Triggertrap/triggertrap-ada/Ada Graphics/Ada Sensor Icons/PDF/fb_890_ada_icon- sound.pdf

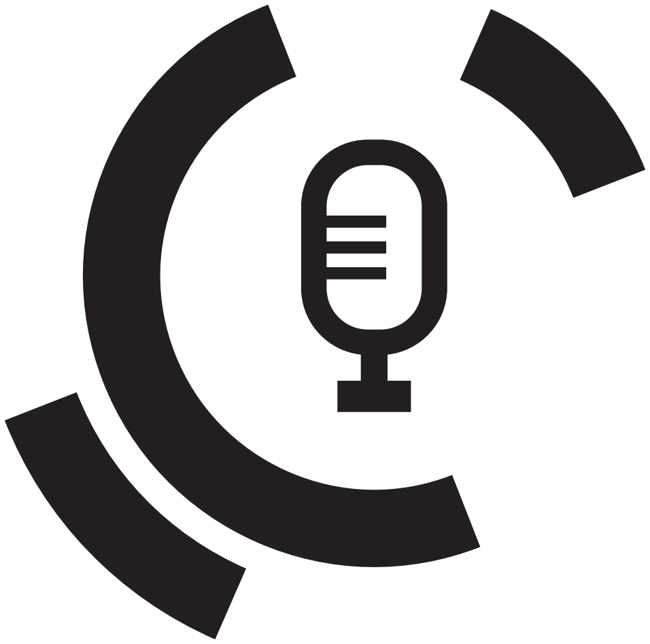
[picture p1: figure]
