Triggertrap/triggertrap-ada/Ada Graphics/Ada Sensor Icons/PDF/fb_890_ada_icon-ambient.pdf

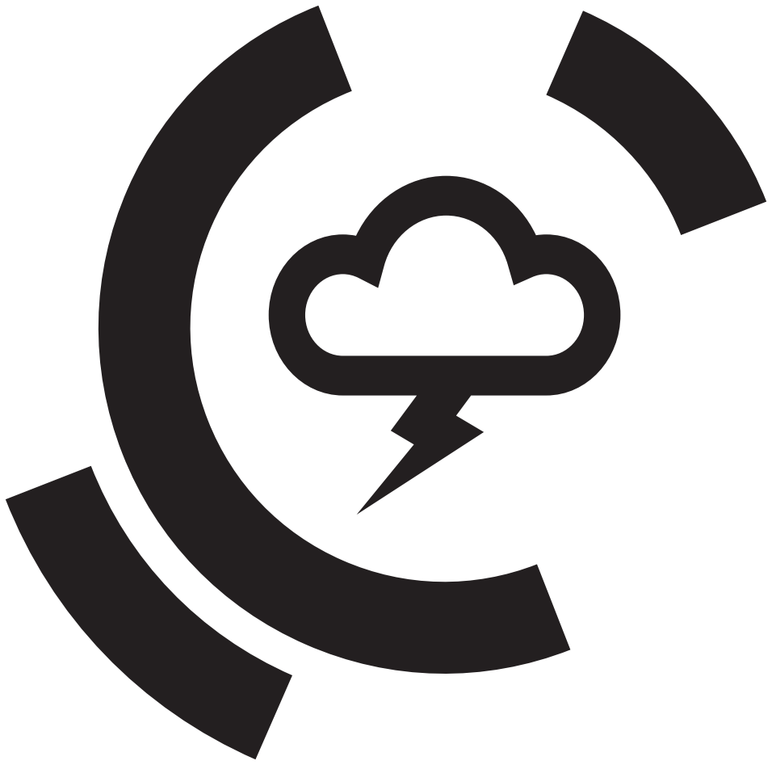
[picture p2: figure]
