Triggertrap/triggertrap-ada/Ada Graphics/Ada Sensor Icons/PDF/fb_890_ada_icon-laser.pdf

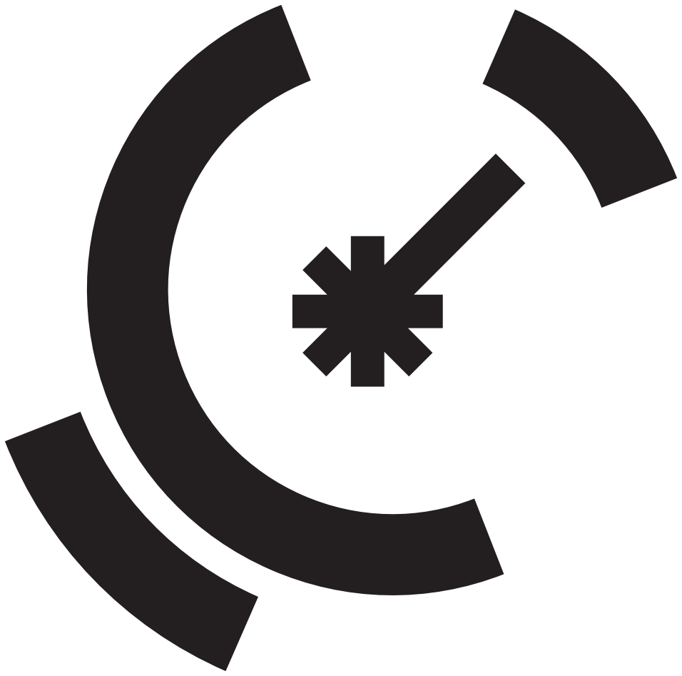
[picture p3: figure]
