Triggertrap/triggertrap-ada/Ada Graphics/Ada Sensor Icons/PDF/fb_890_ada_icon-pir.pdf

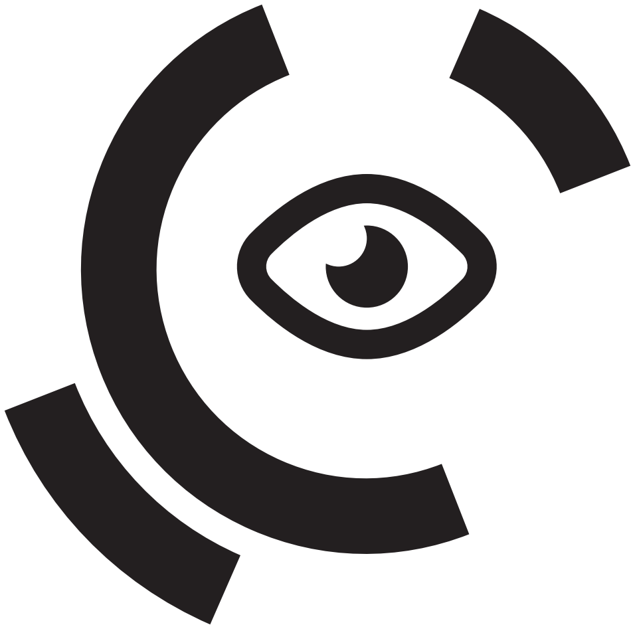
[picture p4: figure]
