Triggertrap/triggertrap-ada/Ada Casing/TT-Issue-A_PDF_mfg_notes/TT-100-A_ADA_BASE_FULL_ASSEMBLY DRG.PDF

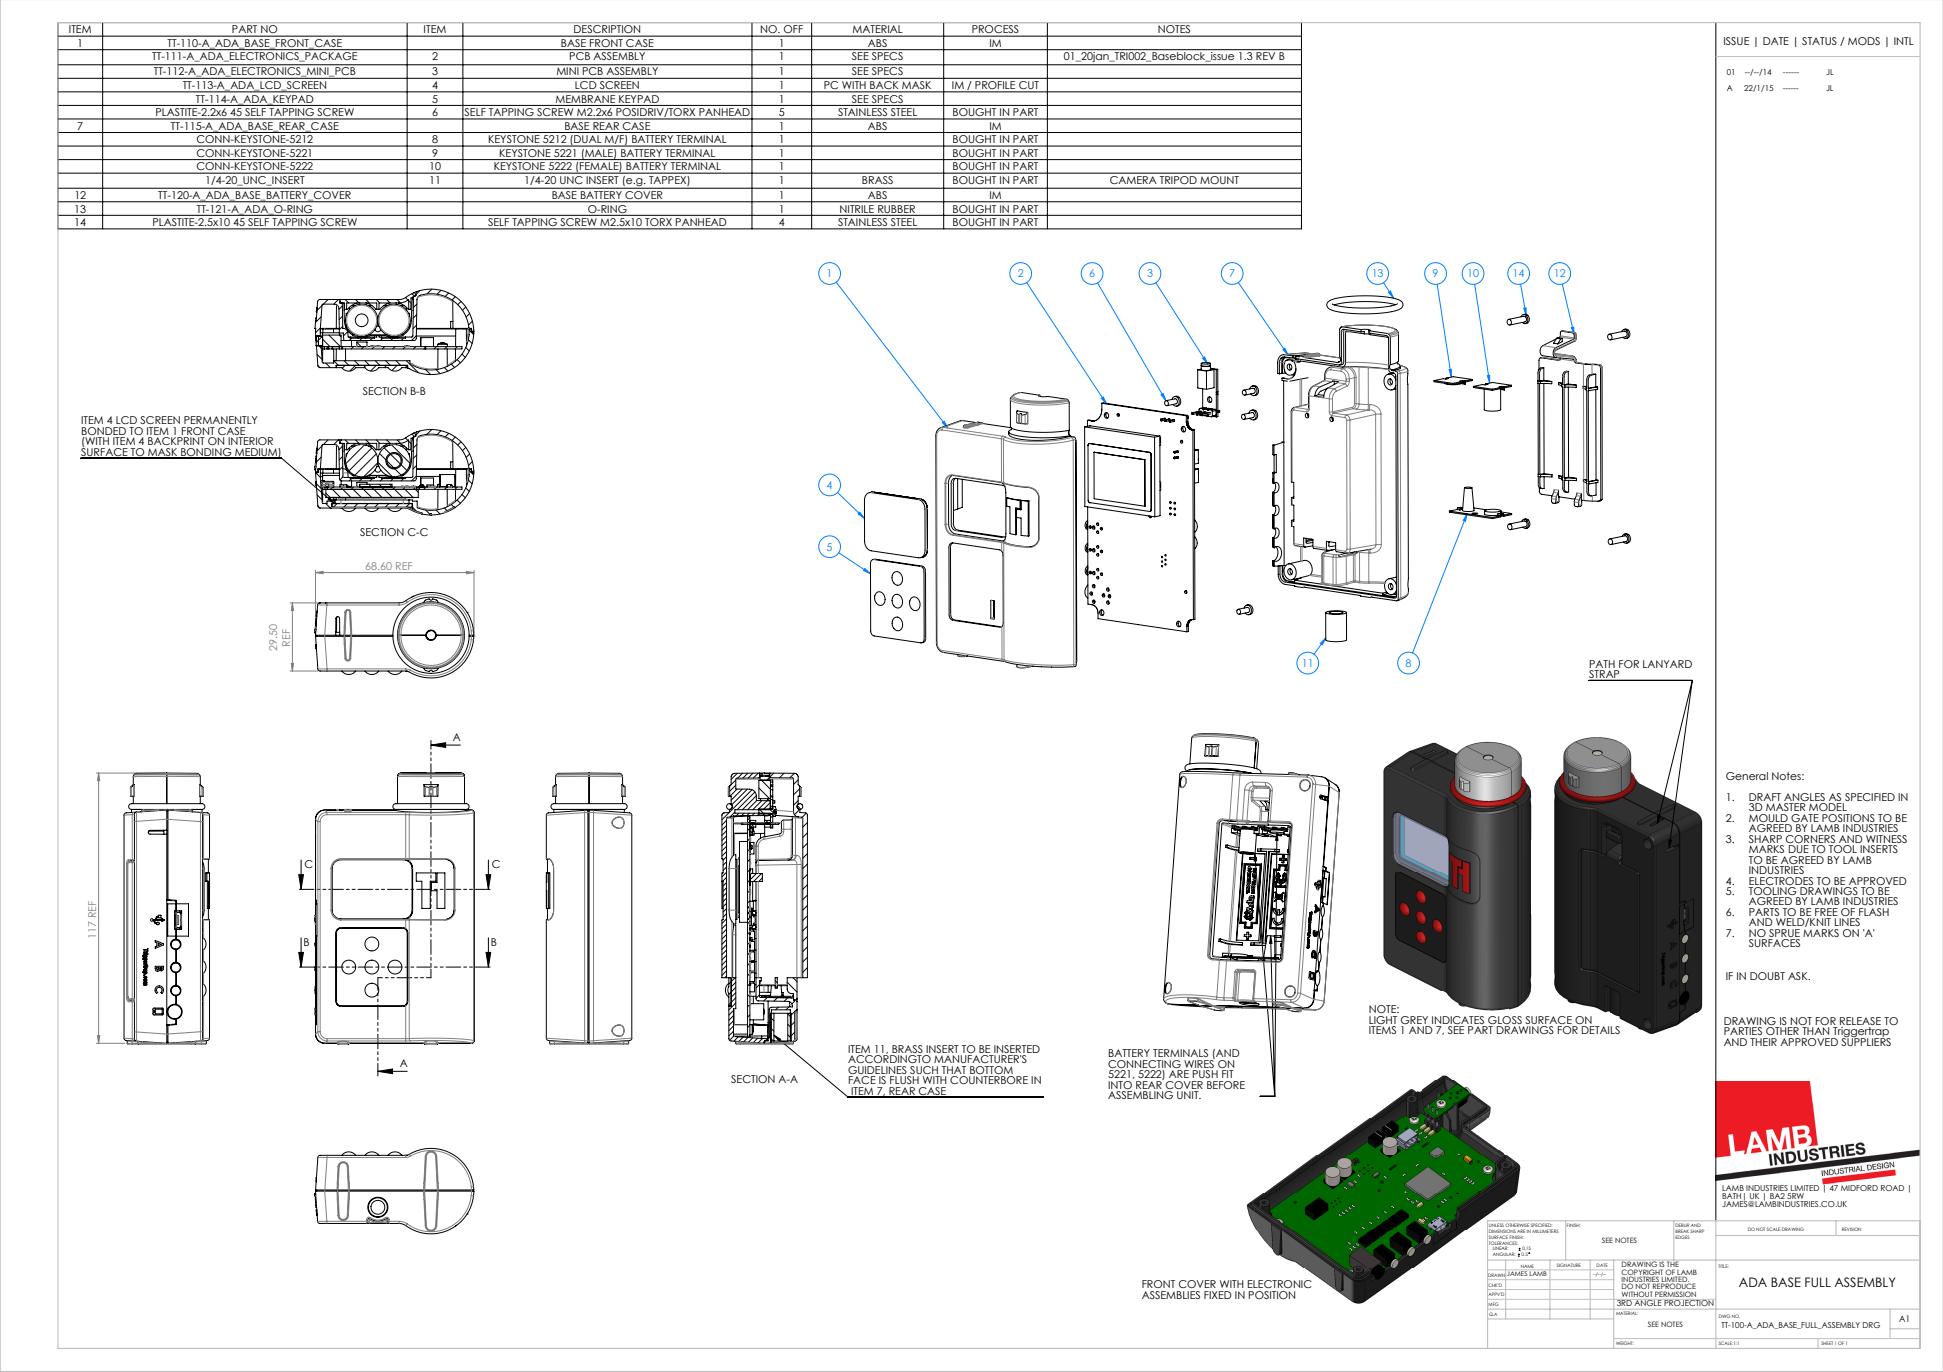
[picture p16: page 1]
117 REF; 68.60 REF; SECTION B-B; SECTION A-A; SECTION C-C; SEE NOTES; SCALE:1:1; SHEET 1 OF 1; DO NOT SCALE DRAWING; REVISION; DEBUR AND BREAK SHARP; UNLESS OTHERWISE SPECIFIED:; FINISH:

ITEM | PART NO | ITEM | DESCRIPTION | NO. OFF | MATERIAL | PROCESS | NOTES | ISSUE | DATE | STATUS / MODS | INTL
1 | TT-110-A_ADA_BASE_FRONT_CASE | | BASE FRONT CASE | 1 | ABS | IM

TT-111-A_ADA_ELECTRONICS_PACKAGE | 2 | PCB ASSEMBLY | 1 | SEE SPECS | | 01_20jan_TRI002_Baseblock_issue 1.3 REV B
TT-112-A_ADA_ELECTRONICS_MINI_PCB | 3 | MINI PCB ASSEMBLY | 1 | SEE SPECS
TT-113-A_ADA_LCD_SCREEN | 4 | LCD SCREEN | 1 | PC WITH BACK MASK | IM / PROFILE CUT
TT-114-A_ADA_KEYPAD | 5 | MEMBRANE KEYPAD | 1 | SEE SPECS
PLASTITE-2.2x6 45 SELF TAPPING SCREW | 6 | SELF TAPPING SCREW M2.2x6 POSIDRIV/TORX PANHEAD | 5 | STAINLESS STEEL | BOUGHT IN PART
CONN-KEYSTONE-5212 | 8 | KEYSTONE 5212 (DUAL M/F) BATTERY TERMINAL | 1 | | BOUGHT IN PART
CONN-KEYSTONE-5221 | 9 | KEYSTONE 5221 (MALE) BATTERY TERMINAL | 1 | | BOUGHT IN PART
CONN-KEYSTONE-5222 | 10 | KEYSTONE 5222 (FEMALE) BATTERY TERMINAL | 1 | | BOUGHT IN PART
1/4-20_UNC_INSERT | 11 | 1/4-20 UNC INSERT (e.g. TAPPEX) | 1 | BRASS | BOUGHT IN PART | CAMERA TRIPOD MOUNT

7 | TT-115-A_ADA_BASE_REAR_CASE | | BASE REAR CASE | 1 | ABS | IM

12 | TT-120-A_ADA_BASE_BATTERY_COVER | | BASE BATTERY COVER | 1 | ABS | IM
13 | TT-121-A_ADA_O-RING | | O-RING | 1 | NITRILE RUBBER | BOUGHT IN PART
14 | PLASTITE-2.5x10 45 SELF TAPPING SCREW | | SELF TAPPING SCREW M2.5x10 TORX PANHEAD | 4 | STAINLESS STEEL | BOUGHT IN PART

ITEM 4 LCD SCREEN PERMANENTLY
BONDED TO ITEM 1 FRONT CASE
(WITH ITEM 4 BACKPRINT ON INTERIOR
SURFACE TO MASK BONDING MEDIUM)

PATH FOR LANYARD
STRAP

General Notes:
1. DRAFT ANGLES AS SPECIFIED IN
3D MASTER MODEL
2. MOULD GATE POSITIONS TO BE
AGREED BY LAMB INDUSTRIES
3. SHARP CORNERS AND WITNESS
MARKS DUE TO TOOL INSERTS
TO BE AGREED BY LAMB
INDUSTRIES
4. ELECTRODES TO BE APPROVED
5. TOOLING DRAWINGS TO BE
6. PARTS TO BE FREE OF FLASH
AND WELD/KNIT LINES
7. NO SPRUE MARKS ON 'A'
SURFACES

IF IN DOUBT ASK.

NOTE:
LIGHT GREY INDICATES GLOSS SURFACE ON
ITEMS 1 AND 7, SEE PART DRAWINGS FOR DETAILS

DRAWING IS NOT FOR RELEASE TO
PARTIES OTHER THAN Triggertrap
AND THEIR APPROVED SUPPLIERS

ITEM 11, BRASS INSERT TO BE INSERTED
ACCORDINGTO MANUFACTURER'S
GUIDELINES SUCH THAT BOTTOM
FACE IS FLUSH WITH COUNTERBORE IN
ITEM 7, REAR CASE

BATTERY TERMINALS (AND
CONNECTING WIRES ON
5221, 5222) ARE PUSH FIT
INTO REAR COVER BEFORE
ASSEMBLING UNIT.

LAMB INDUSTRIES LIMITED | 47 MIDFORD ROAD
BATH| UK | BA2 5RW
JAMES@LAMBINDUSTRIES.CO.UK

DIMENSIONS ARE IN MILLIMETERS
SURFACE FINISH:
TOLERANCES:
ANGULAR: 0.5

NAME | SIGNATURE | DATE | DRAWING IS THE COPYRIGHT OF LAMB INDUSTRIES LIMITED. DO NOT REPRODUCE WITHOUT PERMISSION | TITLE: ADA BASE FULL ASSEMBLY

DRAWN | JAMES LAMB | | --/--/--

FRONT COVER WITH ELECTRONIC
ASSEMBLIES FIXED IN POSITION

CHK'D
APPV'D
MFG | | | | 3RD ANGLE PROJECTION
Q.A | | | | MATERIAL: SEE NOTES | DWG NO. TT-100-A_ADA_BASE_FULL_ASSEMBLY DRG | A1
