Triggertrap/triggertrap-ada/Ada Casing/TT-Issue-A_PDF_mfg_notes/TT-250-A_SENSOR_pot_knob_DRG.PDF

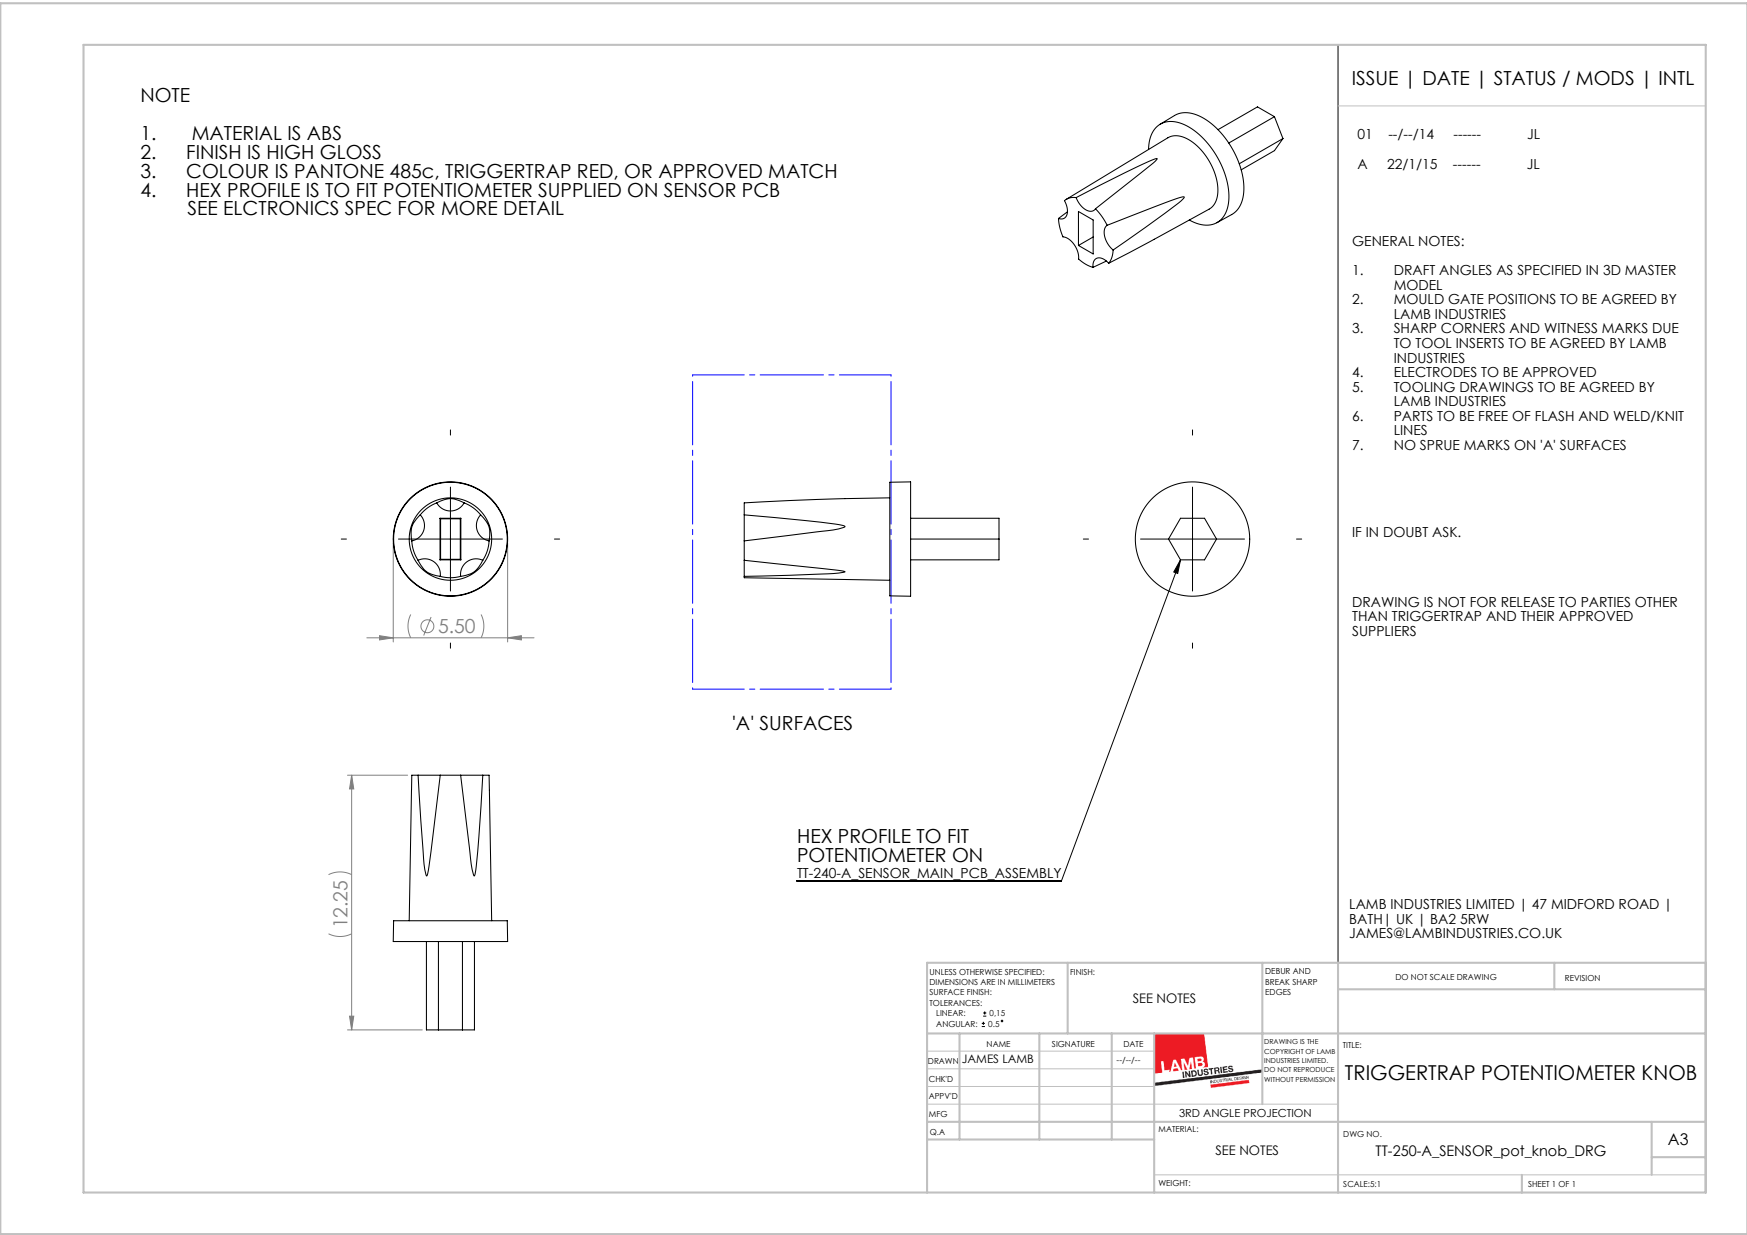
[picture p48: page 1]
'A' SURFACES; SEE NOTES; SCALE:5:1; SHEET 1 OF 1; DO NOT SCALE DRAWING; REVISION; DEBUR AND BREAK SHARP; UNLESS OTHERWISE SPECIFIED:; FINISH:

ISSUE | DATE | STATUS / MODS | INTL

NOTE
1. MATERIAL IS ABS
2. FINISH IS HIGH GLOSS
3. COLOUR IS PANTONE 485c, TRIGGERTRAP RED, OR APPROVED MATCH
4. HEX PROFILE IS TO FIT POTENTIOMETER SUPPLIED ON SENSOR PCB
SEE ELCTRONICS SPEC FOR MORE DETAIL

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

IF IN DOUBT ASK.

DRAWING IS NOT FOR RELEASE TO PARTIES OTHER
THAN TRIGGERTRAP AND THEIR APPROVED
SUPPLIERS

HEX PROFILE TO FIT
POTENTIOMETER ON
TT-240-A_SENSOR_MAIN_PCB_ASSEMBLY

LAMB INDUSTRIES LIMITED | 47 MIDFORD ROAD
BATH| UK | BA2 5RW
JAMES@LAMBINDUSTRIES.CO.UK

DIMENSIONS ARE IN MILLIMETERS
SURFACE FINISH:
TOLERANCES:
ANGULAR: 0.5

NAME | SIGNATURE | DATE | | DRAWING IS THE COPYRIGHT OF LAMB INDUSTRIES LIMITED. DO NOT REPRODUCE WITHOUT PERMISSION | TITLE: TRIGGERTRAP POTENTIOMETER KNOB

DRAWN | JAMES LAMB | | --/--/--

CHK'D
APPV'D
MFG | | | | 3RD ANGLE PROJECTION
Q.A | | | | MATERIAL: SEE NOTES | DWG NO. TT-250-A_SENSOR_pot_knob_DRG | A3
