Triggertrap/triggertrap-ada/Ada Casing/TT-Issue-A_PDF_mfg_notes/TT-260-A-ADA_MIRROR_ASSY_DRG.PDF

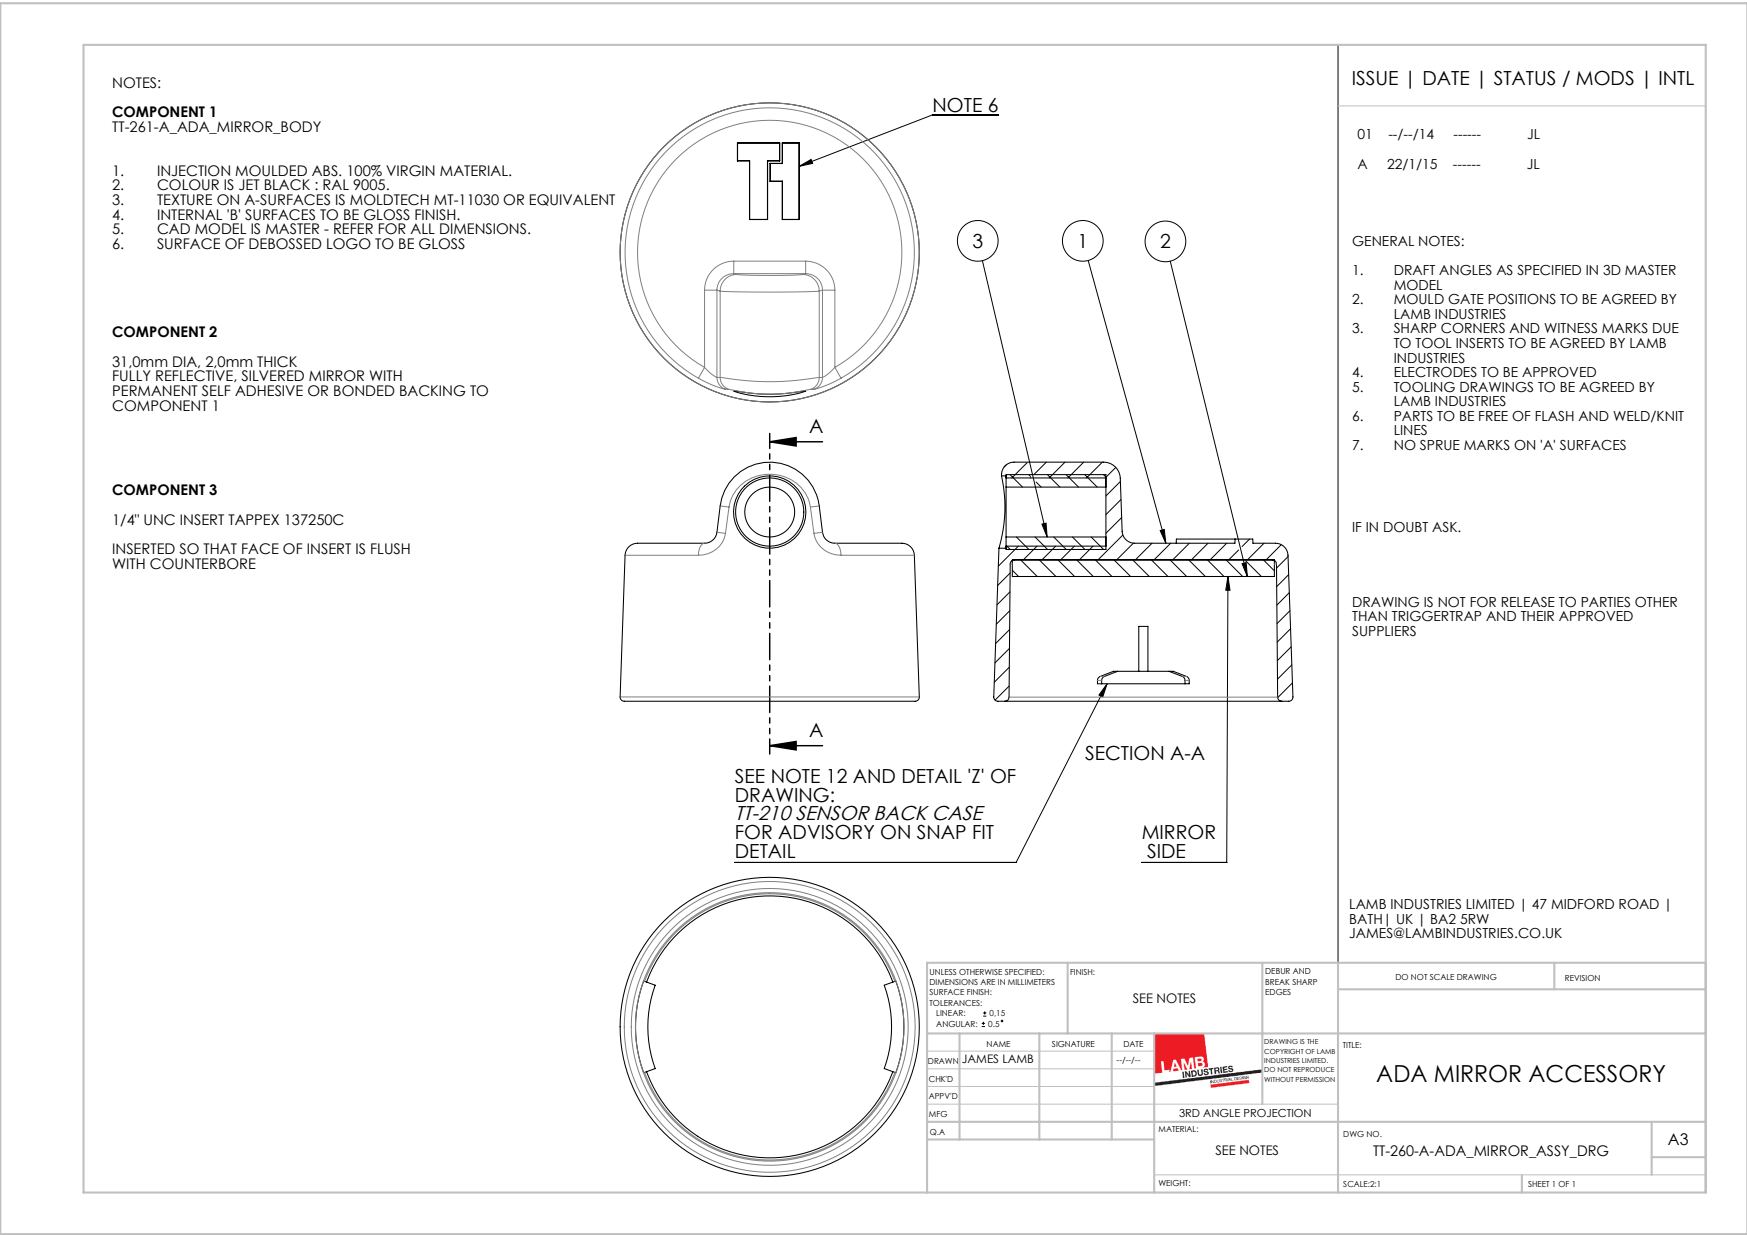
[picture p49: page 1]
NOTE 6; SECTION A-A; COMPONENT 1; SEE NOTES; SCALE:2:1; SHEET 1 OF 1; DO NOT SCALE DRAWING; REVISION; DEBUR AND BREAK SHARP; UNLESS OTHERWISE SPECIFIED:; FINISH:

ISSUE | DATE | STATUS / MODS | INTL

1. INJECTION MOULDED ABS. 100% VIRGIN MATERIAL.
2. COLOUR IS JET BLACK : RAL 9005.
3. TEXTURE ON A-SURFACES IS MOLDTECH MT-11030 OR EQUIVALENT
4. INTERNAL 'B' SURFACES TO BE GLOSS FINISH.
5. CAD MODEL IS MASTER - REFER FOR ALL DIMENSIONS.
6. SURFACE OF DEBOSSED LOGO TO BE GLOSS

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

COMPONENT 2
31,0mm DIA, 2,0mm THICK
FULLY REFLECTIVE, SILVERED MIRROR WITH
PERMANENT SELF ADHESIVE OR BONDED BACKING TO
COMPONENT 1

COMPONENT 3
1/4" UNC INSERT TAPPEX 137250C
INSERTED SO THAT FACE OF INSERT IS FLUSH
WITH COUNTERBORE

IF IN DOUBT ASK.

DRAWING IS NOT FOR RELEASE TO PARTIES OTHER
THAN TRIGGERTRAP AND THEIR APPROVED
SUPPLIERS

SEE NOTE 12 AND DETAIL 'Z' OF
DRAWING:
TT-210 SENSOR BACK CASE
FOR ADVISORY ON SNAP FIT
DETAIL

LAMB INDUSTRIES LIMITED | 47 MIDFORD ROAD
BATH| UK | BA2 5RW
JAMES@LAMBINDUSTRIES.CO.UK

DIMENSIONS ARE IN MILLIMETERS
SURFACE FINISH:
TOLERANCES:
ANGULAR: 0.5

NAME | SIGNATURE | DATE | | DRAWING IS THE COPYRIGHT OF LAMB INDUSTRIES LIMITED. DO NOT REPRODUCE WITHOUT PERMISSION | TITLE: ADA MIRROR ACCESSORY

DRAWN | JAMES LAMB | | --/--/--

CHK'D
APPV'D
MFG | | | | 3RD ANGLE PROJECTION
Q.A | | | | MATERIAL: SEE NOTES | DWG NO. TT-260-A-ADA_MIRROR_ASSY_DRG | A3
