Triggertrap/triggertrap-ada/Triggertrap Ada/TriggerTrap/glcdfont.c

#ifndef FONT5X5_H
#define FONT5X5_H

#ifdef __AVR__
 #include <avr/io.h>
 #include <avr/pgmspace.h>
#else
 #define PROGMEM
#endif
 


// ASCII 5x5 font
#define LCDCHARWIDTH	5
#define LCDCHARHEIGHT	5


static const unsigned char font[] PROGMEM = {
 0x00, 0x00, 0x00, 0x00, 0x00,
 0x02, 0x04, 0x08, 0x04, 0x02,            // Code for char 
 0x08, 0x04, 0x02, 0x04, 0x08,            // Code for char 
 0x00, 0x00, 0x00, 0x00, 0x00,            // Code for char 
 0x00, 0x00, 0x00, 0x00, 0x00,            // Code for char 
 0x00, 0x00, 0x1F, 0x00, 0x00,            // Code for char 
 0x00, 0x00, 0x00, 0x00, 0x00,            // Code for char 
 0x00, 0x00, 0x00, 0x00, 0x00,            // Code for char 
 0x00, 0x00, 0x00, 0x00, 0x00,            // Code for char 
 0x00, 0x00, 0x00, 0x00, 0x00,            // Code for char
 0x00, 0x00, 0x00, 0x00, 0x00,            // Code for char

 0x00, 0x00, 0x00, 0x00, 0x00,            // Code for char
 0x00, 0x00, 0x00, 0x00, 0x00,            // Code for char
 0x00, 0x00, 0x00, 0x00, 0x00,            // Code for char

 0x00, 0x00, 0x00, 0x00, 0x00,            // Code for char 
 0x00, 0x00, 0x00, 0x00, 0x00,            // Code for char 
 0x00, 0x00, 0x00, 0x00, 0x00,            // Code for char 
 0x00, 0x00, 0x00, 0x00, 0x00,            // Code for char 
 0x00, 0x00, 0x00, 0x00, 0x00,            // Code for char 
 0x00, 0x00, 0x00, 0x00, 0x00,            // Code for char 
 0x00, 0x00, 0x00, 0x00, 0x00,            // Code for char 
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
 0x00, 0x00, 0x00, 0x00, 0x00,            // Code for char û
 0x00, 0x00, 0x00, 0x00, 0x00,            // Code for char ü
 0x00, 0x00, 0x00, 0x00, 0x00,            // Code for char ý
 0x00, 0x00, 0x00, 0x00, 0x00             // Code for char þ


};



















#endif 
