Triggertrap/triggertrap-ada/Triggertrap Sensors/TimeDelay.c

/******************************************************************************

File Name:       TimeDelay.c
Dependencies:    None
Processor:       PIC10/PIC12/PIC16/PIC18/PIC24/dsPIC30/dsPIC33/PIC32
Compiler:        PICC, C18, C30, C32
Company:         Microchip Technology, Inc.

Copyright (C) 2011 Microchip Technology Inc.  All rights reserved.

Microchip licenses to you the right to use, modify, copy and distribute 
Software only when embedded on a Microchip microcontroller or digital signal 
controller that is integrated into your product or third party product 
(pursuant to the sublicense terms in the accompanying license agreement).  

You should refer to the license agreement accompanying this Software for 
additional information regarding your rights and obligations.

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
Date        Comments
--------------------------------------------------------------------------------
2009.10.14  File created
2009.10.15  CHANGED C18 DELAY ROUTINE TO DECREMENT ENTIRE NUMBER OF CYCLES
2009.10.19  CHANGED C30 DELAY ROUTINE TO MATCH C18 IMPLEMENTATION
2009.10.26  ADDED C32 DELAY ROUTINE TO MATCH C18 IMPLEMENTATION
2009.10.27  CONSOLIDATED C30 AND C32 IMPLEMENTATIONS, ADDED PADDING TO
            MAKE C30 DELAYS MORE ACCURATE
2010.01.26  Converted locals to volatile 
2010.03.07  Added include "Compiler.h"
2010.10.13  Added PICC support
*******************************************************************************/
#if defined(__PIC32MX__)
    #include <plib.h>
#endif
//#include "Compiler.h"
//#include "HardwareProfile.h"
#include "TimeDelay.h" 

/****************************************************************************
  Function:
    void Delay10us( UINT32 tenMicroSecondCounter )

  Description:
    This routine performs a software delay in intervals of 10 microseconds.

  Precondition:
    None

  Parameters:
    UINT32 tenMicroSecondCounter - number of ten microsecond delays
    to perform at once.

  Returns:
    None

  Remarks:
    None
  ***************************************************************************/
void Delay10us( UINT32 tenMicroSecondCounter )
{
    volatile INT32 cyclesRequiredForEntireDelay;    
        
    #if defined(__18CXX) || defined (COMPILER_HITECH_PICC)
    
        if (GetInstructionClock() <= 2500000) //for all FCY speeds under 2MHz (FOSC <= 10MHz)
        {
            //26 cycles burned through this path (includes return to caller).
            //For FOSC == 1MHZ, it takes 104us.
            //For FOSC == 4MHZ, it takes 26us
            //For FOSC == 8MHZ, it takes 13us.
            //For FOSC == 10MHZ, it takes 10.5us.
        }
        else
        {
            //14 cycles burned to this point.
            
            //We want to pre-calculate number of cycles required to delay 10us * tenMicroSecondCounter using a 1 cycle granule.
            cyclesRequiredForEntireDelay = (INT32)(GetInstructionClock()/100000) * tenMicroSecondCounter;
            
            //We subtract all the cycles used up until we reach the while loop below, where each loop cycle count is subtracted.
            //Also we subtract the 22 cycle function return.
            cyclesRequiredForEntireDelay -= (153 + 22);
            
            if (cyclesRequiredForEntireDelay <= 45)
            {
                // If we have exceeded the cycle count already, bail! Best compromise between FOSC == 12MHz and FOSC == 24MHz.
            }    
            else
            {
                //Try as you may, you can't get out of this heavier-duty case under 30us. ;]
                
                while (cyclesRequiredForEntireDelay>0) //153 cycles used to this point.
                {
                    Nop(); //Delay one instruction cycle at a time, not absolutely necessary.
                    cyclesRequiredForEntireDelay -= 42; //Subtract cycles burned while doing each delay stage, 42 in this case.
                }
            }
        }
    
    #elif defined(__C30__) || defined(__PIC32MX__)
    
        if(GetInstructionClock() <= 500000) //for all FCY speeds under 500KHz (FOSC <= 1MHz)
        {
            //10 cycles burned through this path (includes return to caller).
            //For FOSC == 1MHZ, it takes 5us.
            //For FOSC == 4MHZ, it takes 0.5us
            //For FOSC == 8MHZ, it takes 0.25us.
            //For FOSC == 10MHZ, it takes 0.2us.
        }    
        else
        {
            //7 cycles burned to this point.
            
            //We want to pre-calculate number of cycles required to delay 10us * tenMicroSecondCounter using a 1 cycle granule.
            cyclesRequiredForEntireDelay = (INT32)(GetInstructionClock()/100000)*tenMicroSecondCounter;
            
            #if defined(__C30__)
                //We subtract all the cycles used up until we reach the while loop below, where each loop cycle count is subtracted.
                //Also we subtract the 5 cycle function return.
                cyclesRequiredForEntireDelay -= 44; //(29 + 5) + 10 cycles padding
            #elif defined(__PIC32MX__)
                //We subtract all the cycles used up until we reach the while loop below, where each loop cycle count is subtracted.
                //Also we subtract the 5 cycle function return.
                cyclesRequiredForEntireDelay -= 24; //(19 + 5)
            #endif
            
            if(cyclesRequiredForEntireDelay <= 0)
            {
                // If we have exceeded the cycle count already, bail!
            }
            else
            {   
                while(cyclesRequiredForEntireDelay>0) //19 cycles used to this point.
                {
                    #if defined(__C30__)
                        cyclesRequiredForEntireDelay -= 11; //Subtract cycles burned while doing each delay stage, 12 in this case. Add one cycle as padding.
                    #elif defined(__PIC32MX__)
                        cyclesRequiredForEntireDelay -= 8; //Subtract cycles burned while doing each delay stage, 8 in this case.
                    #endif
                }
            }
        }
    #endif
}

/****************************************************************************
  Function:
    void DelayMs( UINT16 ms )

  Description:
    This routine performs a software delay in intervals of 1 millisecond.

  Precondition:
    None

  Parameters:
    UINT16 ms - number of one millisecond delays to perform at once.

  Returns:
    None

  Remarks:
    None
  ***************************************************************************/
void DelayMs( UINT16 ms )
{
    #if defined(__18CXX) || defined (COMPILER_HITECH_PICC)
        
        INT32 cyclesRequiredForEntireDelay;
        
        // We want to pre-calculate number of cycles required to delay 1ms, using a 1 cycle granule.
        cyclesRequiredForEntireDelay = (signed long)(GetInstructionClock()/1000) * ms;
        
        // We subtract all the cycles used up until we reach the while loop below, where each loop cycle count is subtracted.
        // Also we subtract the 22 cycle function return.
        cyclesRequiredForEntireDelay -= (148 + 22);

        if (cyclesRequiredForEntireDelay <= (170+25)) 
        {
            return;     // If we have exceeded the cycle count already, bail!
        }    
        else
        {
            while (cyclesRequiredForEntireDelay > 0) //148 cycles used to this point.
            {
                Nop();                              // Delay one instruction cycle at a time, not absolutely necessary.
                cyclesRequiredForEntireDelay -= 39; // Subtract cycles burned while doing each delay stage, 39 in this case.
            }
        }
        
    #elif defined(__C30__) || defined(__PIC32MX__)
    
        volatile UINT8 i;
        
        while (ms--)
        {
            i = 4;
            while (i--)
            {
                Delay10us( 25 );
            }
        }
    #endif
}
