Triggertrap/triggertrap-ada/Triggertrap Ada/TriggerTrap/WInterrupts.c

/* -*- mode: jde; c-basic-offset: 2; indent-tabs-mode: nil -*- */

/*
  Part of the Wiring project - http://wiring.uniandes.edu.co

  Copyright (c) 2004-05 Hernando Barragan

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
  Modified 24 November 2006 by David A. Mellis
*/

#include <inttypes.h>
#include <avr/io.h>
#include <avr/interrupt.h>
#include <avr/pgmspace.h>
#include <stdio.h>

#include "wiring_private.h"

static volatile voidFuncPtr intFunc[EXTERNAL_NUM_INTERRUPTS];
static uint8_t portLastValue[EXTERNAL_NUM_INTERRUPTS/8];
// volatile static voidFuncPtr twiIntFunc;

uint8_t getBitFromBitField(uint8_t input)
{
  switch(input)
  {
  case 0x1:
	return 0;
  case 0x2:
	return 1;
  case 0x4:
    return 2;
  case 0x8:
	return 3;
  case 0x10:
	return 4;
  case 0x20:
    return 5;
  case 0x40:
    return 6;
  case 0x80:
    return 7;
  default:
    return 0;
  }
}

void attachInterrupt(uint8_t interruptNum, void (*userFunc)(void), int mode) {
  if( EXTERNAL_NUM_INTERRUPTS <= interruptNum ) {
      return;
  }
  
  //Convert arduino mode value to the XMega mode value
  switch(mode)
  {
	case LOW:
		mode = 3;
		break;
	case CHANGE:
		mode = 0;
		break;
	case RISING:
		mode = 1;
		break;
	case FALLING:
		mode = 2;
		break;
	case LEVEL:
		mode = 3;
		break;
	default:
		mode = 0;
		break;
  }
  
  // Configure the interrupt mode (trigger on low input, any change, rising
  // edge, or falling edge).  The mode constants were chosen to correspond
  // to the configuration bits in the hardware register, so we simply shift
  // the mode into place.

  // Enable the interrupt.
  uint8_t  portIndex = digitalPinToPort(interruptNum);
  PORT_t*  port      = (PORT_t*)portRegister(portIndex);
  uint8_t* pinctrl   = (uint8_t*)&port->PIN0CTRL;

  uint8_t pin = getBitFromBitField(digitalPinToBitMask(interruptNum));
  // put intFunc in sorted order
  intFunc[(digitalPinToPort(interruptNum)-1)*8+pin] = userFunc;

  port->INTCTRL  |= PORT_INT1LVL_LO_gc;
  port->INT1MASK |= digitalPinToBitMask(interruptNum);
  pinctrl[pin]   |= mode;
  portLastValue[portIndex] = port->IN;
}

void detachInterrupt(uint8_t interruptNum) {
  if( EXTERNAL_NUM_INTERRUPTS <= interruptNum ) {
      return;
  }
      
  uint8_t  portIndex = digitalPinToPort(interruptNum);
  PORT_t*  port      = (PORT_t*)portRegister(portIndex);
  uint8_t* pinctrl   = (uint8_t*)&port->PIN0CTRL;

  uint8_t pin = getBitFromBitField(digitalPinToBitMask(interruptNum));

  intFunc[(digitalPinToPort(interruptNum)-1)*8+pin] = 0;
  port->INT1MASK &= ~(digitalPinToBitMask(interruptNum));
  if ( 0 == port->INT1MASK ) {
    // No interrupts on any of ports pins, turn it off.
    port->INTCTRL &= ~PORT_INT1LVL_gm;
  }
  pinctrl[pin] &= ~PORT_ISC_gm;
}

void PORT_INT( int portIndex )
{
  PORT_t*  port    = (PORT_t*)portRegister(portIndex);
  uint8_t* pinctrl = (uint8_t*)&port->PIN0CTRL;
  uint8_t  value   = port->IN;
  uint8_t  prev    = portLastValue[portIndex];
  uint8_t  pin     = (portIndex-1)*8;

  portLastValue[portIndex] = value;

  int     index;
  for ( index = 0; index < 8; ++index ) {
    int     valueHigh = value&1;
    int     valueLow  = !valueHigh;
    int     prevHigh  = prev&1;
    int     prevLow   = !prevHigh;
    int     falling   = prevHigh && valueLow;
    int     rising    = prevLow  && valueHigh;
    int     changing  = prevLow  != valueLow;
    uint8_t mode      = *pinctrl & PORT_ISC_gm;
    int     call      = 0;

    if ( 0 == intFunc[pin] ) {
        // Nothing to do
        call = 0;
    } else if ( PORT_ISC_BOTHEDGES_gc==mode && changing ) {
        call = 1;
    } else if ( PORT_ISC_RISING_gc==mode && rising ) {
        call = 1;
    } else if ( PORT_ISC_FALLING_gc==mode && falling ) {
        call = 1;
    } else if ( PORT_ISC_LEVEL_gc==mode && valueLow ) {
        call = 1;
    }
    if ( call ) {
      intFunc[pin]();
    }
    value >>= 1;
    prev  >>= 1;
    ++pin;
    ++pinctrl;
  }

  port->INTFLAGS &= ~PORT_INT1IF_bm;
}

						//Removed the arduino version of this int 
ISR(PORTA_INT1_vect)
{
  PORT_INT(PA);
}

ISR(PORTB_INT1_vect)
{
  PORT_INT(PB);
}

ISR(PORTC_INT1_vect)
{
  PORT_INT(PC);
}

ISR(PORTD_INT1_vect)
{
  PORT_INT(PD);
}

ISR(PORTE_INT1_vect)
{
  PORT_INT(PE);
}

#if defined(PORTF)
ISR(PORTF_INT1_vect)
{
  PORT_INT(PF);
}
#endif
